229Lee229/Scanner/Program-MDK/Bootloader/PRJ/STM32F10x_AN2557_FW_V3.3.0/Project/IAP/src/main.c

/**
  ******************************************************************************
  * @file    IAP/src/main.c 
  * @author  MCD Application Team
  * @version V3.3.0
  * @date    10/15/2010
  * @brief   Main program body
  ******************************************************************************
  * @copy
  *
  * THE PRESENT FIRMWARE WHICH IS FOR GUIDANCE ONLY AIMS AT PROVIDING CUSTOMERS
  * WITH CODING INFORMATION REGARDING THEIR PRODUCTS IN ORDER FOR THEM TO SAVE
  * TIME. AS A RESULT, STMICROELECTRONICS SHALL NOT BE HELD LIABLE FOR ANY
  * DIRECT, INDIRECT OR CONSEQUENTIAL DAMAGES WITH RESPECT TO ANY CLAIMS ARISING
  * FROM THE CONTENT OF SUCH FIRMWARE AND/OR THE USE MADE BY CUSTOMERS OF THE
  * CODING INFORMATION CONTAINED HEREIN IN CONNECTION WITH THEIR PRODUCTS.
  *
  * <h2><center>&copy; COPYRIGHT 2010 STMicroelectronics</center></h2>
  */ 

/** @addtogroup IAP
  * @{
  */

/* Includes ------------------------------------------------------------------*/
#include "common.h"
#include "stdbool.h"
/* Private typedef -----------------------------------------------------------*/
/* Private define ------------------------------------------------------------*/
/* Private macro -------------------------------------------------------------*/
/* Private variables ---------------------------------------------------------*/
extern pFunction Jump_To_Application;
extern uint32_t JumpAddress;
FLASH_Status Erase_Flag_Sector(void);
/* Private function prototypes -----------------------------------------------*/
static void IAP_Init(void);
// #define FlagAddress 0x08002C00
/* Private functions ---------------------------------------------------------*/

/**
  * @brief  Main program.
  * @param  None
  * @retval None
  */
int main(void)
{
	uint32_t flag = *(volatile uint32_t*)0x08002C00;
	bool boot = false;
	if(flag == 0xFFFFFFFF)	boot = false;
	else{
		boot = true;
		Erase_Flag_Sector();
		int i;
		for(i = 0; i <= 10000;i++);
	}
  /* Flash unlock */
  FLASH_Unlock();

  /* Initialize Key Button mounted on STM3210X-EVAL board */       
  STM_EVAL_PBInit(BUTTON_KEY, BUTTON_MODE_GPIO);   
  /* Test if Key push-button on STM3210X-EVAL Board is pressed */
   // if (STM_EVAL_PBGetState(BUTTON_KEY)  == 0x00)

	// 正常运行
   if(boot == false)
	{ 
    /* Test if user code is programmed starting from address "ApplicationAddress" */
		if (((*(__IO uint32_t*)ApplicationAddress) & 0x2FFE0000 ) == 0x20000000)
		{ 
		  /* Jump to user application */
		  JumpAddress = *(__IO uint32_t*) (ApplicationAddress + 4);
		  Jump_To_Application = (pFunction) JumpAddress;
		  /* Initialize user application's Stack Pointer */
		  __set_MSP(*(__IO uint32_t*) ApplicationAddress);
		  Jump_To_Application();
		}
	}
  else
  {
	IAP_Init();
    SerialPutString("\r\n======================================================================");
    SerialPutString("\r\n=              (C) COPYRIGHT 2010 STMicroelectronics                 =");
    SerialPutString("\r\n=                                                                    =");
    SerialPutString("\r\n=     In-Application Programming Application  (Version 3.3.0)        =");
    SerialPutString("\r\n=                                                                    =");
    SerialPutString("\r\n=                                   By MCD Application Team          =");
    SerialPutString("\r\n======================================================================");
    SerialPutString("\r\n\r\n");
    Main_Menu ();
  }

  while (1)
  {}
}

FLASH_Status Erase_Flag_Sector(void)
{
    FLASH_Status status = FLASH_COMPLETE;
    
    /* ??Flash */
    FLASH_Unlock();
    
    /* ???????? */
    FLASH_ClearFlag(FLASH_FLAG_BSY | FLASH_FLAG_EOP | FLASH_FLAG_PGERR | FLASH_FLAG_WRPRTERR);
    
    /* ????? */
    status = FLASH_ErasePage(0x08002C00);
    
    /* ????Flash */
    FLASH_Lock();
    
    return status;
}

/**
  * @brief  Initialize the IAP: Configure RCC, USART and GPIOs.
  * @param  None
  * @retval None
  */
void IAP_Init(void)
{
 USART_InitTypeDef USART_InitStructure;

  /* USART resources configuration (Clock, GPIO pins and USART registers) ----*/
  /* USART configured as follow:
        - BaudRate = 115200 baud  
        - Word Length = 8 Bits
        - One Stop Bit
        - No parity
        - Hardware flow control disabled (RTS and CTS signals)
        - Receive and transmit enabled
  */
  USART_InitStructure.USART_BaudRate = 115200;
  USART_InitStructure.USART_WordLength = USART_WordLength_8b;
  USART_InitStructure.USART_StopBits = USART_StopBits_1;
  USART_InitStructure.USART_Parity = USART_Parity_No;
  USART_InitStructure.USART_HardwareFlowControl = USART_HardwareFlowControl_None;
  USART_InitStructure.USART_Mode = USART_Mode_Rx | USART_Mode_Tx;

  STM_EVAL_COMInit(COM1, &USART_InitStructure);  
}

#ifdef USE_FULL_ASSERT
/**
  * @brief  Reports the name of the source file and the source line number
  *         where the assert_param error has occurred.
  * @param  file: pointer to the source file name
  * @param  line: assert_param error line source number
  * @retval None
  */
void assert_failed(uint8_t* file, uint32_t line)
{
  /* User can add his own implementation to report the file name and line number,
     ex: printf("Wrong parameters value: file %s on line %d\r\n", file, line) */

  /* Infinite loop */
  while (1)
  {
  }
}
#endif

/**
  * @}
  */

/******************* (C) COPYRIGHT 2010 STMicroelectronics *****END OF FILE****/
