229Lee229/Scanner/Program-MDK/Bootloader/PRJ/STM32F10x_AN2557_FW_V3.3.0/Project/IAP/inc/common.h

/**
  ******************************************************************************
  * @file    IAP/inc/common.h 
  * @author  MCD Application Team
  * @version V3.3.0
  * @date    10/15/2010
  * @brief   This file provides all the headers of the common functions.
  ******************************************************************************
  * @copy
  *
  * THE PRESENT FIRMWARE WHICH IS FOR GUIDANCE ONLY AIMS AT PROVIDING CUSTOMERS
  * WITH CODING INFORMATION REGARDING THEIR PRODUCTS IN ORDER FOR THEM TO SAVE
  * TIME. AS A RESULT, STMICROELECTRONICS SHALL NOT BE HELD LIABLE FOR ANY
  * DIRECT, INDIRECT OR CONSEQUENTIAL DAMAGES WITH RESPECT TO ANY CLAIMS ARISING
  * FROM THE CONTENT OF SUCH FIRMWARE AND/OR THE USE MADE BY CUSTOMERS OF THE
  * CODING INFORMATION CONTAINED HEREIN IN CONNECTION WITH THEIR PRODUCTS.
  *
  * <h2><center>&copy; COPYRIGHT 2010 STMicroelectronics</center></h2>
  */ 

/* Define to prevent recursive inclusion -------------------------------------*/
#ifndef _COMMON_H
#define _COMMON_H

/* Includes ------------------------------------------------------------------*/
#include "stdio.h"
#include "string.h"
#include "stm32f10x.h"
#include "ymodem.h"
#include "stm32_eval.h" 

/* Exported types ------------------------------------------------------------*/
typedef  void (*pFunction)(void);

/* Exported constants --------------------------------------------------------*/
/* Constants used by Serial Command Line Mode */
#define CMD_STRING_SIZE       128

#define ApplicationAddress    0x8003000

#if defined (STM32F10X_MD) || defined (STM32F10X_MD_VL)
 #define PAGE_SIZE                         (0x400)    /* 1 Kbyte */
 #define FLASH_SIZE                        (0x10000)  /* 128 KBytes */
#elif defined STM32F10X_CL
 #define PAGE_SIZE                         (0x800)    /* 2 Kbytes */
 #define FLASH_SIZE                        (0x40000)  /* 256 KBytes */
#elif defined STM32F10X_HD || defined (STM32F10X_HD_VL)
 #define PAGE_SIZE                         (0x800)    /* 2 Kbytes */
 #define FLASH_SIZE                        (0x80000)  /* 512 KBytes */
#elif defined STM32F10X_XL
 #define PAGE_SIZE                         (0x800)    /* 2 Kbytes */
 #define FLASH_SIZE                        (0x100000) /* 1 MByte */
#else 
 #error "Please select first the STM32 device to be used (in stm32f10x.h)"    
#endif

/* Compute the FLASH upload image size */  
#define FLASH_IMAGE_SIZE                   (uint32_t) (FLASH_SIZE - (ApplicationAddress - 0x08000000))

/* Exported macro ------------------------------------------------------------*/
/* Common routines */
#define IS_AF(c)  ((c >= 'A') && (c <= 'F'))
#define IS_af(c)  ((c >= 'a') && (c <= 'f'))
#define IS_09(c)  ((c >= '0') && (c <= '9'))
#define ISVALIDHEX(c)  IS_AF(c) || IS_af(c) || IS_09(c)
#define ISVALIDDEC(c)  IS_09(c)
#define CONVERTDEC(c)  (c - '0')

#define CONVERTHEX_alpha(c)  (IS_AF(c) ? (c - 'A'+10) : (c - 'a'+10))
#define CONVERTHEX(c)   (IS_09(c) ? (c - '0') : CONVERTHEX_alpha(c))

#define SerialPutString(x) Serial_PutString((uint8_t*)(x))

/* Exported functions ------------------------------------------------------- */
void Int2Str(uint8_t* str,int32_t intnum);
uint32_t Str2Int(uint8_t *inputstr,int32_t *intnum);
uint32_t GetIntegerInput(int32_t * num);
uint32_t SerialKeyPressed(uint8_t *key);
uint8_t GetKey(void);
void SerialPutChar(uint8_t c);
void Serial_PutString(uint8_t *s);
void GetInputString(uint8_t * buffP);
uint32_t FLASH_PagesMask(__IO uint32_t Size);
void FLASH_DisableWriteProtectionPages(void);
void Main_Menu(void);
void SerialDownload(void);
void SerialUpload(void);

#endif  /* _COMMON_H */

/*******************(C)COPYRIGHT 2010 STMicroelectronics *****END OF FILE******/
